mattaperkins/2FA_Sidecar/images/IMG_0535.jpeg

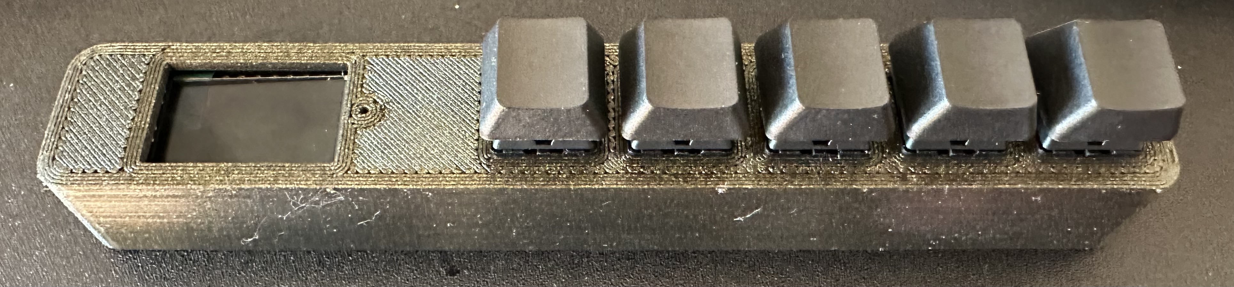
images/IMG_0535.jpeg
